nekoraa/NekoSlime/过程图片/1755057824756--511587132.jpg

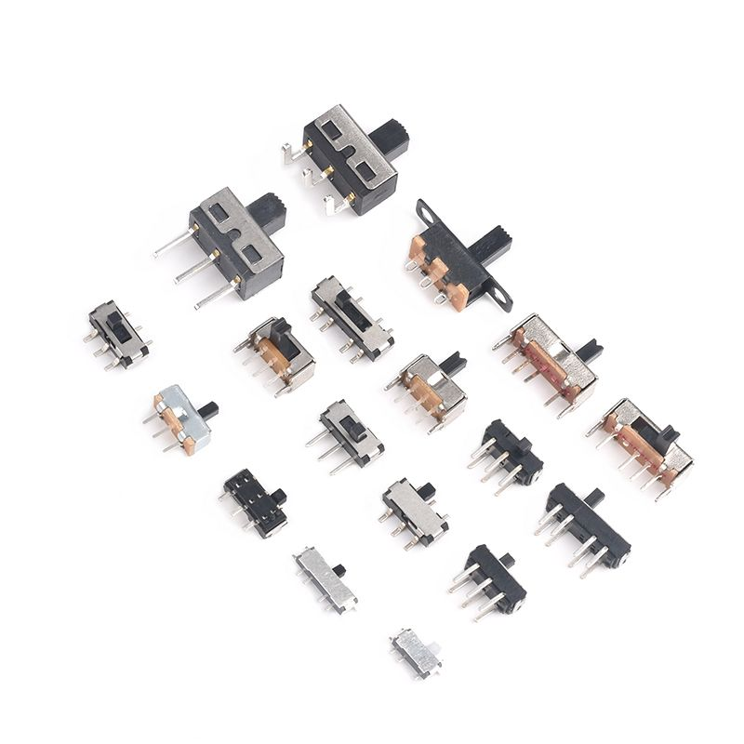
过程图片/1755057824756--511587132.jpg
